CWRUbotix/Micromouse-2023-24/software/Mouse/Algo/API.h

#include <stdio.h>
#include <stdlib.h>
#include <string.h>

int mazeWidth();
int mazeHeight();

int wallFront();
int wallRight();
int wallLeft();

int moveForward(int spaces);  // Returns 0 if crash, else returns 1
void movingTurnRight();
void movingTurnLeft();
void turnRight();
void turnLeft();
void turnRight45();
void turnLeft45();
void turn180();

void setWall(int x, int y, char direction);
void clearWall(int x, int y, char direction);

void setColor(int x, int y, char color);
void clearColor(int x, int y);
void clearAllColor();

void setText(int x, int y, char* str);
void clearText(int x, int y);
void clearAllText();

int wasReset();
void ackReset();
