CWRUbotix/Micromouse-2023-24/software/Arduino-dev/micromouse-floodfill/LeftWallFollow.c

/**
 * @file Converted.c
 * @author kaleb
 * @brief ripped this left-wall follow from mms-c
 * @date 2023-11-10
 * 
 * I thought documentation would be cool or useful
 */

#include <stdio.h>

#include "API.h"

void log(char* text) {
    fprintf(stderr, "%s\n", text);
    fflush(stderr);
}

int main(int argc, char* argv[]) {
    log("Running...");
    API_setColor(0, 0, 'G');
    API_setText(0, 0, "abc");
    while (1) {
        if (!API_wallLeft()) {
            API_turnLeft();
        }
        while (API_wallFront()) {
            API_turnRight();
        }
        API_moveForward();
    }
}
